TRocacher/SolarDeviceManagement_2023/RemoteDevice/Dev_Soft_RemoteDevice_L031/Core/Src/StandByWkUpPgm.c

#include "StandByWkupPgm.h"

/* =================================================================================
* ==================   Main_StandByWkUpPgm	     ===========================================
  General Configurations (Clock, all io, I2C1, ADC1 ain6)
  Si Pwr reset ou BP reset
  	  FactoryReset
  Sinon (wkup RTC depuis Standby Mode)
  	  StandByWkUpPgm
  FinSi

* =================================================================================*/

static void MX_ADC_Init(void);

void Main_StandByWkUpPgm(void)
{
/***************************************************************
			Configurations spécifique Wkup StdBy
***************************************************************/

/***************************************************************
			Mesure température
***************************************************************/

/***************************************************************
			Emission Info UC, attente réception UC
***************************************************************/


/***************************************************************
			Mise à jour Climatiseur
***************************************************************/


/***************************************************************
			Ajustement RTC
***************************************************************/



}



/***************************************************************
		ADC1 Ain6
***************************************************************/
static void MX_ADC_Init(void)
{
  LL_ADC_REG_InitTypeDef ADC_REG_InitStruct = {0};
  LL_ADC_InitTypeDef ADC_InitStruct = {0};
  /* Peripheral clock enable */
  LL_APB2_GRP1_EnableClock(LL_APB2_GRP1_PERIPH_ADC1);
  LL_IOP_GRP1_EnableClock(LL_IOP_GRP1_PERIPH_GPIOA);
  //ADC GPIO Configuration voir RmDv_IO.c

  // Configure Regular Channel
  LL_ADC_REG_SetSequencerChAdd(ADC1, LL_ADC_CHANNEL_6);
  /** Common config  */
  ADC_REG_InitStruct.TriggerSource = LL_ADC_REG_TRIG_SOFTWARE;
  ADC_REG_InitStruct.SequencerDiscont = LL_ADC_REG_SEQ_DISCONT_DISABLE;
  ADC_REG_InitStruct.ContinuousMode = LL_ADC_REG_CONV_SINGLE;
  ADC_REG_InitStruct.DMATransfer = LL_ADC_REG_DMA_TRANSFER_NONE;
  ADC_REG_InitStruct.Overrun = LL_ADC_REG_OVR_DATA_PRESERVED;
  LL_ADC_REG_Init(ADC1, &ADC_REG_InitStruct);
  LL_ADC_SetSamplingTimeCommonChannels(ADC1, LL_ADC_SAMPLINGTIME_1CYCLE_5);
  LL_ADC_SetOverSamplingScope(ADC1, LL_ADC_OVS_DISABLE);
  LL_ADC_REG_SetSequencerScanDirection(ADC1, LL_ADC_REG_SEQ_SCAN_DIR_FORWARD);
  LL_ADC_SetCommonFrequencyMode(__LL_ADC_COMMON_INSTANCE(ADC1), LL_ADC_CLOCK_FREQ_MODE_HIGH);
  LL_ADC_DisableIT_EOC(ADC1);
  LL_ADC_DisableIT_EOS(ADC1);
  ADC_InitStruct.Clock = LL_ADC_CLOCK_SYNC_PCLK_DIV2;
  ADC_InitStruct.Resolution = LL_ADC_RESOLUTION_12B;
  ADC_InitStruct.DataAlignment = LL_ADC_DATA_ALIGN_RIGHT;
  ADC_InitStruct.LowPowerMode = LL_ADC_LP_MODE_NONE;
  LL_ADC_Init(ADC1, &ADC_InitStruct);

  /* Enable ADC internal voltage regulator */
  LL_ADC_EnableInternalRegulator(ADC1);
  /* Delay for ADC internal voltage regulator stabilization. */
  /* Compute number of CPU cycles to wait for, from delay in us. */
  /* Note: Variable divided by 2 to compensate partially */
  /* CPU processing cycles (depends on compilation optimization). */
  /* Note: If system core clock frequency is below 200kHz, wait time */
  /* is only a few CPU processing cycles. */
  uint32_t wait_loop_index;
  wait_loop_index = ((LL_ADC_DELAY_INTERNAL_REGUL_STAB_US * (SystemCoreClock / (100000 * 2))) / 10);
  while(wait_loop_index != 0)
  {
    wait_loop_index--;
  }
}
