TRocacher/SolarDeviceManagement_2023/RemoteDevice/Dev_Soft_RemoteDevice_L031/Core/Inc/StandByWkUpPgm.h

/*
 * StandByWkUpPgm.h
 *
 *  Created on: 16 juil. 2023
 *      Author: trocache
 */

#include "main.h"

#ifndef INC_STANDBYWKUPPGM_H_
#define INC_STANDBYWKUPPGM_H_

void Main_StandByWkUpPgm(void);

#endif /* INC_STANDBYWKUPPGM_H_ */
