TRocacher/SolarDeviceManagement_2023/ComStack/KEIL_F103/Stack_Src_103/Timer_F103.h

#ifndef _TIMER_F103_H__
#define _TIMER_F103_H__


#include "stm32f10x.h"


void SystickStart(void);
int SystickGet(void);

void MyTimer_IT_Enable( TIM_TypeDef *Timer, char Prio, void (*IT_function) (void));
void MyTimer_CkEnable(TIM_TypeDef *Timer);
void MyTimer_Set_Period(TIM_TypeDef *Timer, int ARR, int PSC );

#endif
